mcb77/mc68000_sbc/kicad/mc68000_sbc.kicad_sch

## KiCad design kicad/mc68000_sbc.kicad_sch (2025-10-26)

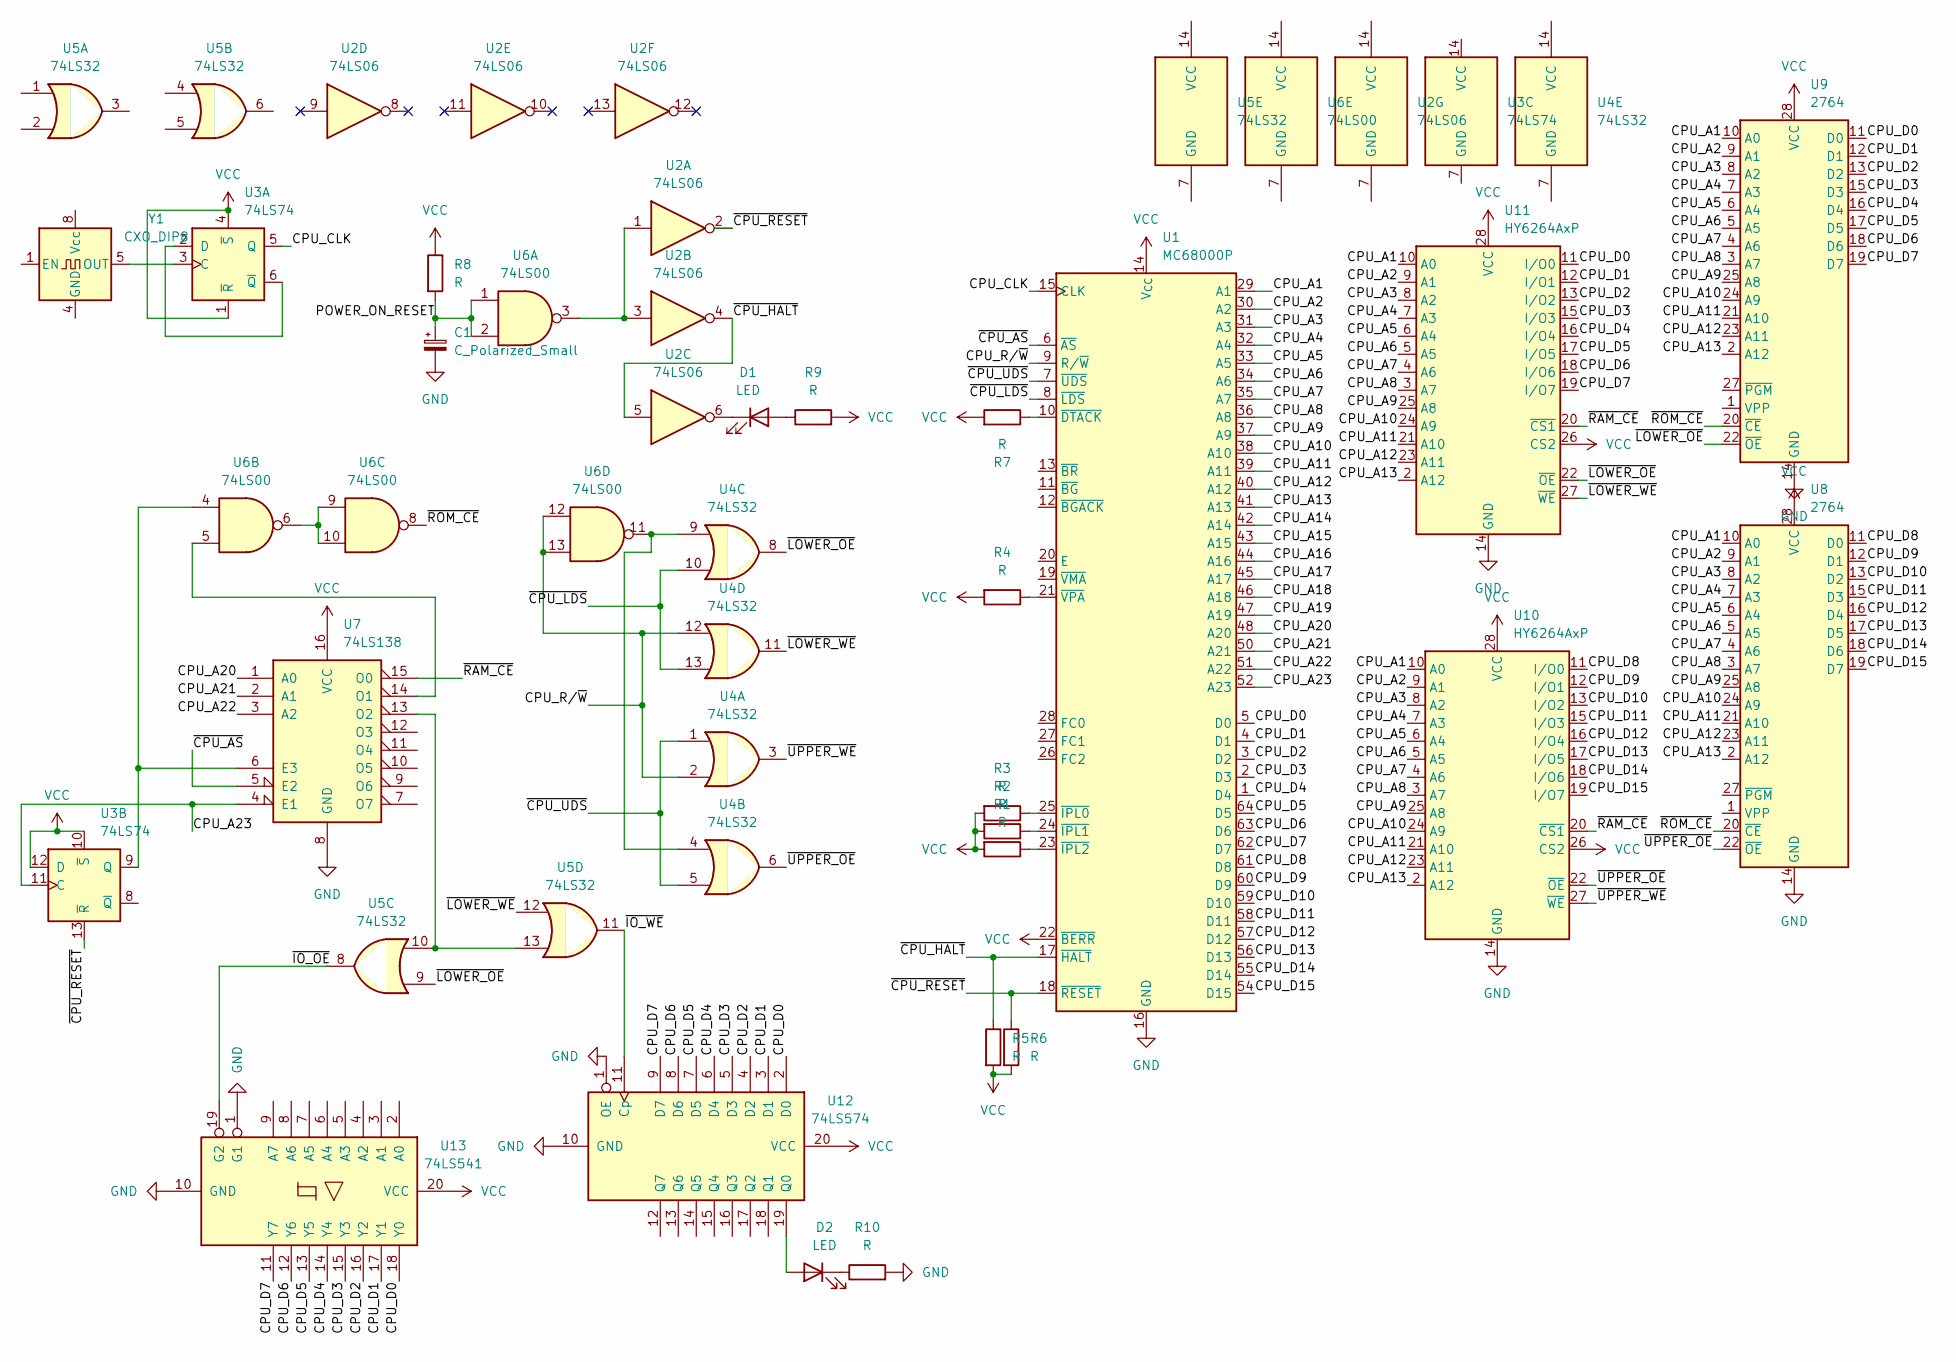
[picture p2: schematic mc68000_sbc.kicad_sch]

Parts:
C1: C_Polarized_Small; CP_Radial_D6.3mm_P2.50mm
D1, D2: LED; LED_D3.0mm
R1, R2, R3, R4, R5, R6, R7, R8, R9, R10: R; R_Axial_DIN0204_L3.6mm_D1.6mm_P7.62mm_Horizontal
U1: MC68000P; DIP-64_W22.86mm_Socket
U2: 74LS06; DIP-14_W7.62mm_Socket
U3: 74LS74; DIP-14_W7.62mm_Socket
U4: 74LS32; DIP-14_W7.62mm_Socket
U5: 74LS32
U6: 74LS00; DIP-14_W7.62mm_Socket
U7: 74LS138; DIP-16_W7.62mm_Socket
U8, U9: 2764; DIP-28_W15.24mm_Socket
U10, U11: HY6264AxP; DIP-28_W15.24mm_Socket
U12: 74LS574; DIP-20_W7.62mm_Socket
U13: 74LS541; DIP-20_W7.62mm_Socket
Y1: CXO_DIP8; Oscillator_DIP-8

Connections:
CPU_A1: U1.29 (A1), U8.10 (A0), U9.10 (A0), U10.10 (A0), U11.10 (A0)
CPU_A2: U1.30 (A2), U8.9 (A1), U9.9 (A1), U10.9 (A1), U11.9 (A1)
CPU_A3: U1.31 (A3), U8.8 (A2), U9.8 (A2), U10.8 (A2), U11.8 (A2)
CPU_A4: U1.32 (A4), U8.7 (A3), U9.7 (A3), U10.7 (A3), U11.7 (A3)
CPU_A5: U1.33 (A5), U8.6 (A4), U9.6 (A4), U10.6 (A4), U11.6 (A4)
CPU_A6: U1.34 (A6), U8.5 (A5), U9.5 (A5), U10.5 (A5), U11.5 (A5)
CPU_A7: U1.35 (A7), U8.4 (A6), U9.4 (A6), U10.4 (A6), U11.4 (A6)
CPU_A8: U1.36 (A8), U8.3 (A7), U9.3 (A7), U10.3 (A7), U11.3 (A7)
CPU_A9: U1.37 (A9), U8.25 (A8), U9.25 (A8), U10.25 (A8), U11.25 (A8)
CPU_A10: U1.38 (A10), U8.24 (A9), U9.24 (A9), U10.24 (A9), U11.24 (A9)
CPU_A11: U1.39 (A11), U8.21 (A10), U9.21 (A10), U10.21 (A10), U11.21 (A10)
CPU_A12: U1.40 (A12), U8.23 (A11), U9.23 (A11), U10.23 (A11), U11.23 (A11)
CPU_A13: U1.41 (A13), U8.2 (A12), U9.2 (A12), U10.2 (A12), U11.2 (A12)
CPU_A14: U1.42 (A14)
CPU_A15: U1.43 (A15)
CPU_A16: U1.44 (A16)
CPU_A17: U1.45 (A17)
CPU_A18: U1.46 (A18)
CPU_A19: U1.47 (A19)
CPU_A20: U1.48 (A20), U7.1 (A0)
CPU_A21: U1.50 (A21), U7.2 (A1)
CPU_A22: U1.51 (A22), U7.3 (A2)
CPU_A23: U1.52 (A23), U3.11 (C), U7.4 (E1)
CPU_CLK: U1.15 (CLK), U3.5 (Q)
CPU_D0: U1.5 (D0), U9.11 (D0), U11.11 (I/O0), U12.2 (D0), U13.18 (Y0)
CPU_D1: U1.4 (D1), U9.12 (D1), U11.12 (I/O1), U12.3 (D1), U13.17 (Y1)
CPU_D2: U1.3 (D2), U9.13 (D2), U11.13 (I/O2), U12.4 (D2), U13.16 (Y2)
CPU_D3: U1.2 (D3), U9.15 (D3), U11.15 (I/O3), U12.5 (D3), U13.15 (Y3)
CPU_D4: U1.1 (D4), U9.16 (D4), U11.16 (I/O4), U12.6 (D4), U13.14 (Y4)
CPU_D5: U1.64 (D5), U9.17 (D5), U11.17 (I/O5), U12.7 (D5), U13.13 (Y5)
CPU_D6: U1.63 (D6), U9.18 (D6), U11.18 (I/O6), U12.8 (D6), U13.12 (Y6)
CPU_D7: U1.62 (D7), U9.19 (D7), U11.19 (I/O7), U12.9 (D7), U13.11 (Y7)
CPU_D8: U1.61 (D8), U8.11 (D0), U10.11 (I/O0)
CPU_D9: U1.60 (D9), U8.12 (D1), U10.12 (I/O1)
CPU_D10: U1.59 (D10), U8.13 (D2), U10.13 (I/O2)
CPU_D11: U1.58 (D11), U8.15 (D3), U10.15 (I/O3)
CPU_D12: U1.57 (D12), U8.16 (D4), U10.16 (I/O4)
CPU_D13: U1.56 (D13), U8.17 (D5), U10.17 (I/O5)
CPU_D14: U1.55 (D14), U8.18 (D6), U10.18 (I/O6)
CPU_D15: U1.54 (D15), U8.19 (D7), U10.19 (I/O7)
CPU_R/~W: U1.9 (R/~W), U4.2, U4.12, U6.12, U6.13
GND: C1.2, R10.2, U1.16 (GND), U1.53 (GND), U7.8 (GND), U8.14 (GND), U9.14 (GND), U10.14 (GND), U11.14 (GND), U12.1 (OE), U12.10 (GND), U13.1 (G1), U13.10 (GND)
unnamed: D1.1 (K), U2.6
unnamed: D1.2 (A), R9.1
unnamed: D2.1 (K), R10.1
unnamed: D2.2 (A), U12.19 (Q0)
unnamed: R1.1, U1.23 (~IPL2)
unnamed: R2.1, U1.24 (~IPL1)
unnamed: R3.1, U1.25 (~IPL0)
unnamed: R4.1, U1.21 (~VPA)
unnamed: R7.1, U1.10 (~DTACK)
unnamed: U2.1, U2.3, U6.3
unnamed: U3.2 (D), U3.6 (~Q)
unnamed: U3.3 (C), Y1.5 (OUT)
unnamed: U3.9 (Q), U6.4, U7.6 (E3)
unnamed: U4.4, U4.9, U6.11
unnamed: U5.10, U5.13, U7.13 (O2)
unnamed: U6.5, U7.14 (O1)
unnamed: U6.6, U6.9, U6.10
POWER_ON_RESET: C1.1, R8.2, U6.1, U6.2
VCC: R1.2, R2.2, R3.2, R4.2, R5.2, R6.2, R7.2, R8.1, R9.2, U1.14 (V_{CC}), U1.22 (~BERR), U1.49 (V_{CC}), U3.1 (~R), U3.4 (~S), U3.10 (~S), U3.12 (D), U7.16 (VCC), U8.28 (VCC), U9.28 (VCC), U10.26 (CS2), U10.28 (VCC), U11.26 (CS2), U11.28 (VCC), U12.20 (VCC), U13.20 (VCC)
~CPU_AS: U1.6 (~AS), U7.5 (E2)
~CPU_HALT: R5.1, U1.17 (~HALT), U2.4, U2.5
~CPU_LDS: U1.8 (~LDS), U4.10, U4.13
~CPU_RESET: R6.1, U1.18 (~RESET), U2.2, U3.13 (~R)
~CPU_UDS: U1.7 (~UDS), U4.1, U4.5
~IO_OE: U5.8, U13.19 (G2)
~IO_WE: U5.11, U12.11 (Cp)
~LOWER_OE: U4.8, U5.9, U9.22 (~OE), U11.22 (~OE)
~LOWER_WE: U4.11, U5.12, U11.27 (~WE)
~RAM_CE: U7.15 (O0), U10.20 (~CS1), U11.20 (~CS1)
~ROM_CE: U6.8, U8.20 (~CE), U9.20 (~CE)
~UPPER_OE: U4.6, U8.22 (~OE), U10.22 (~OE)
~UPPER_WE: U4.3, U10.27 (~WE)
